maplac/rpi_meteo/electronics/sensor_A_revA_production/bottom.jpg

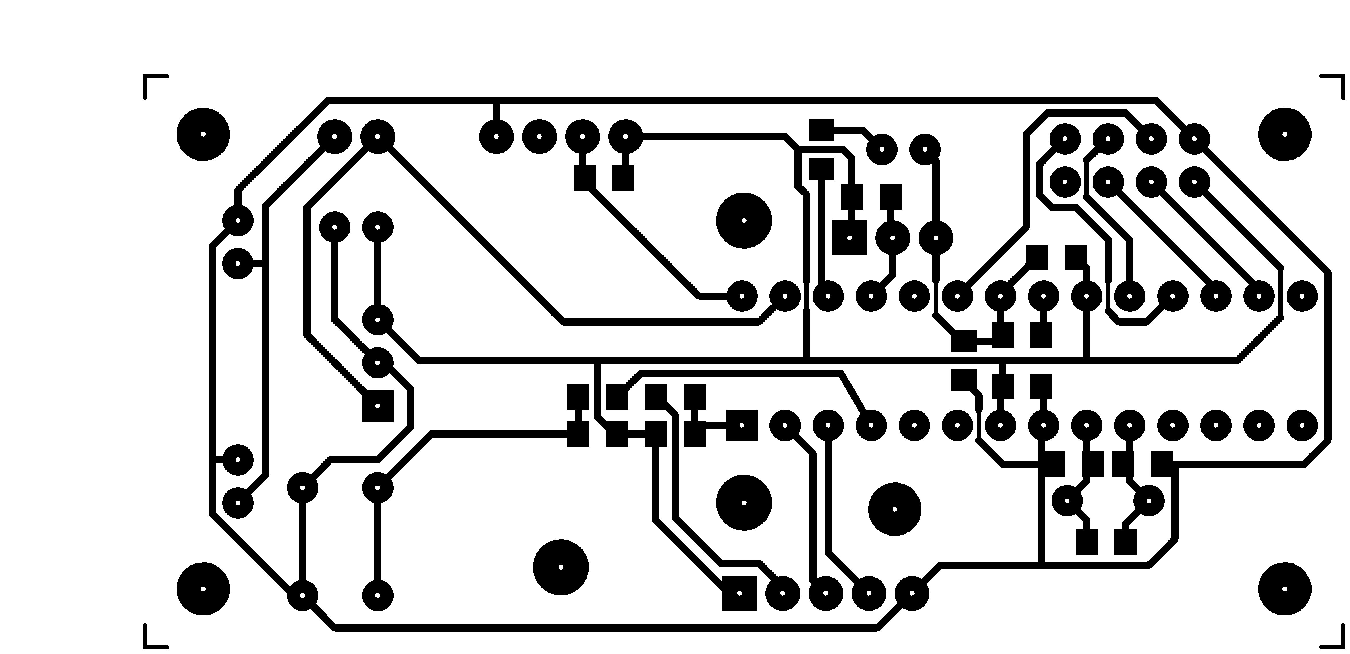
electronics/sensor_A_revA_production/bottom.jpg
