maplac/rpi_meteo/photos/base_bottom_revA.jpg

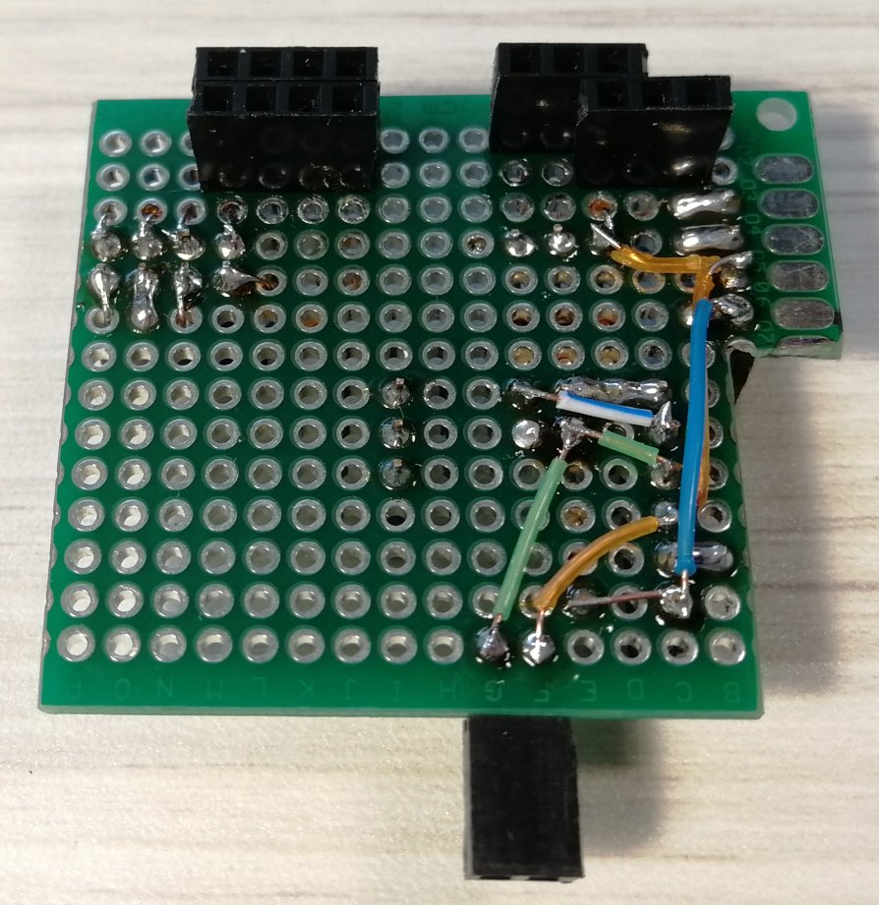
photos/base_bottom_revA.jpg
