maplac/rpi_meteo/photos/base_populated_revA.jpg

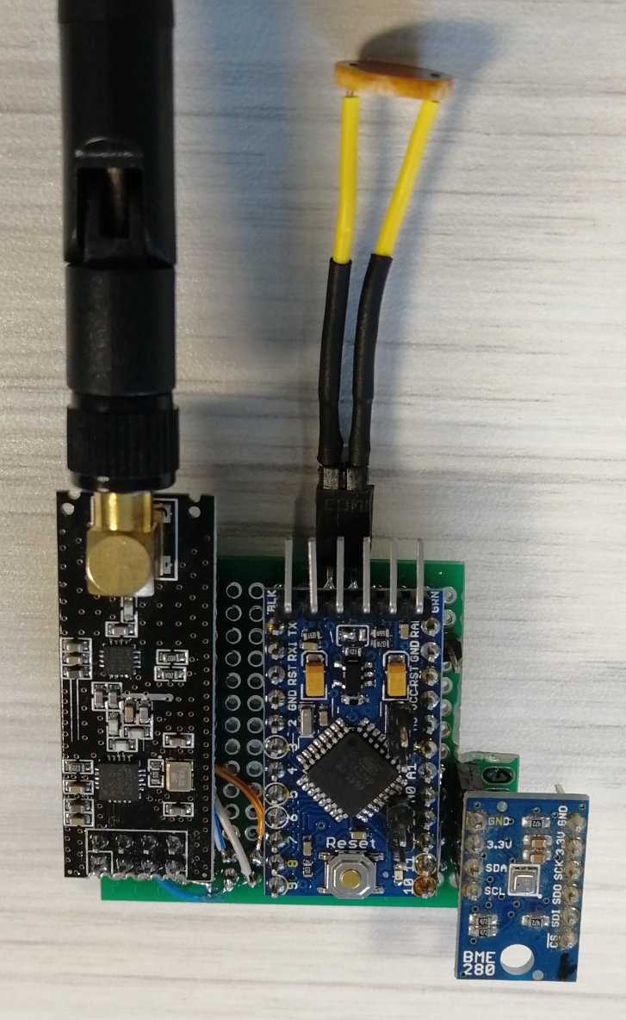
photos/base_populated_revA.jpg
