maplac/rpi_meteo/photos/rpi_meteo_back_revA.jpg

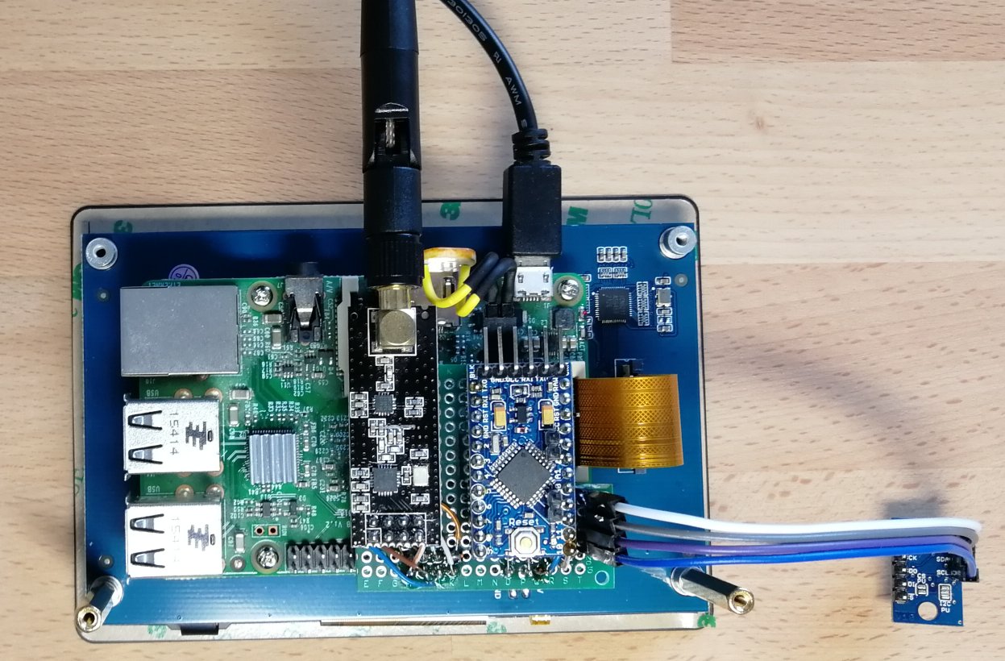
photos/rpi_meteo_back_revA.jpg
