maplac/rpi_meteo/photos/rpi_meteo_front_revA.jpg

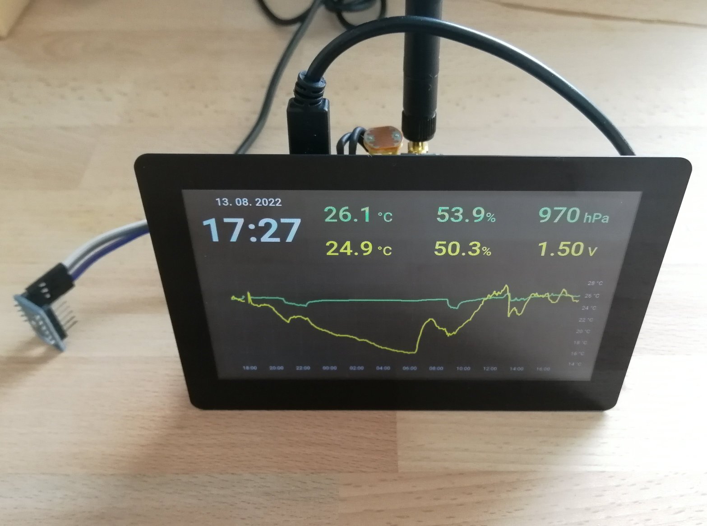
photos/rpi_meteo_front_revA.jpg
