maplac/rpi_meteo/photos/sensor_A_populated_bottom_revA.jpg

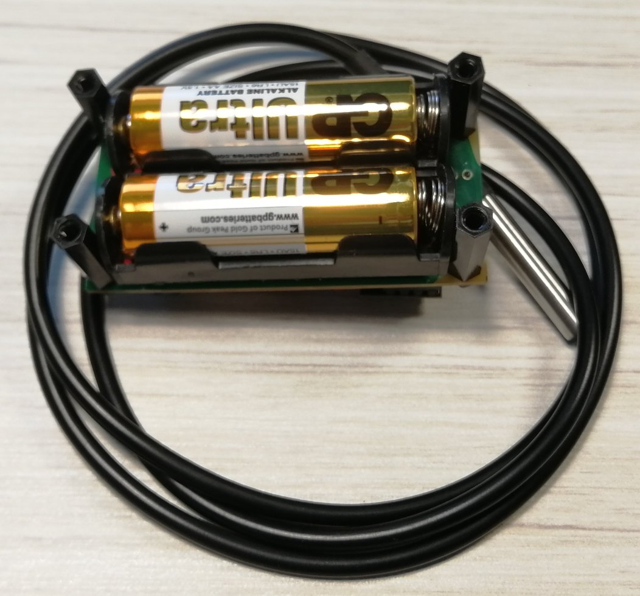
photos/sensor_A_populated_bottom_revA.jpg
