maplac/rpi_meteo/photos/sensor_A_populated_top_revA.jpg

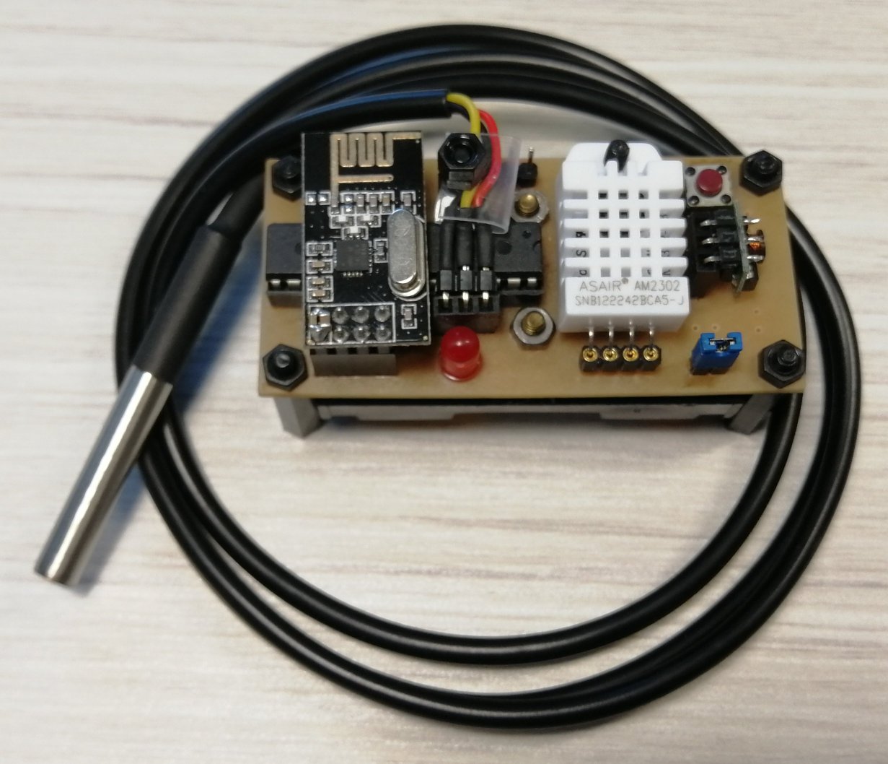
photos/sensor_A_populated_top_revA.jpg
